muonTelescope/glowcost-geiger/cad/models/C142864/preview.png

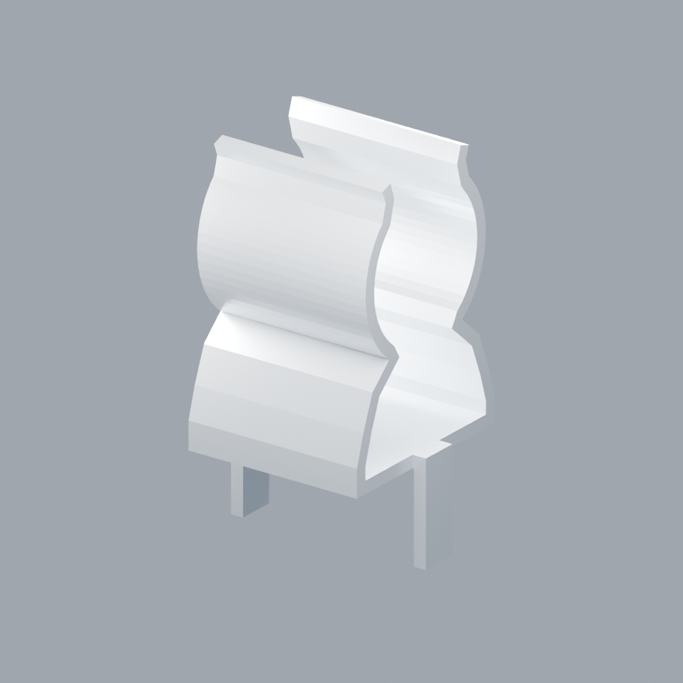
cad/models/C142864/preview.png
