muonTelescope/glowcost-geiger/cad/models/C142864/C142864.FCStd

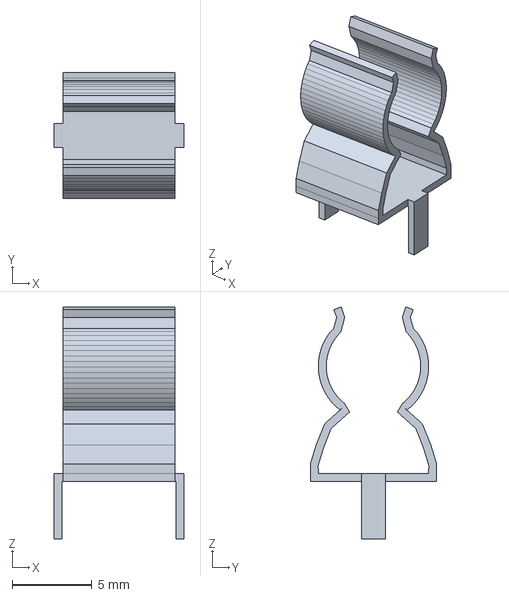
[picture p31: CAD file, 2026-09-16]
cad/models/C142864/C142864.FCStd
8.10 x 7.90 x 14.5 mm
